Kshitij-1030/ClawMind/cad/xaxis.step

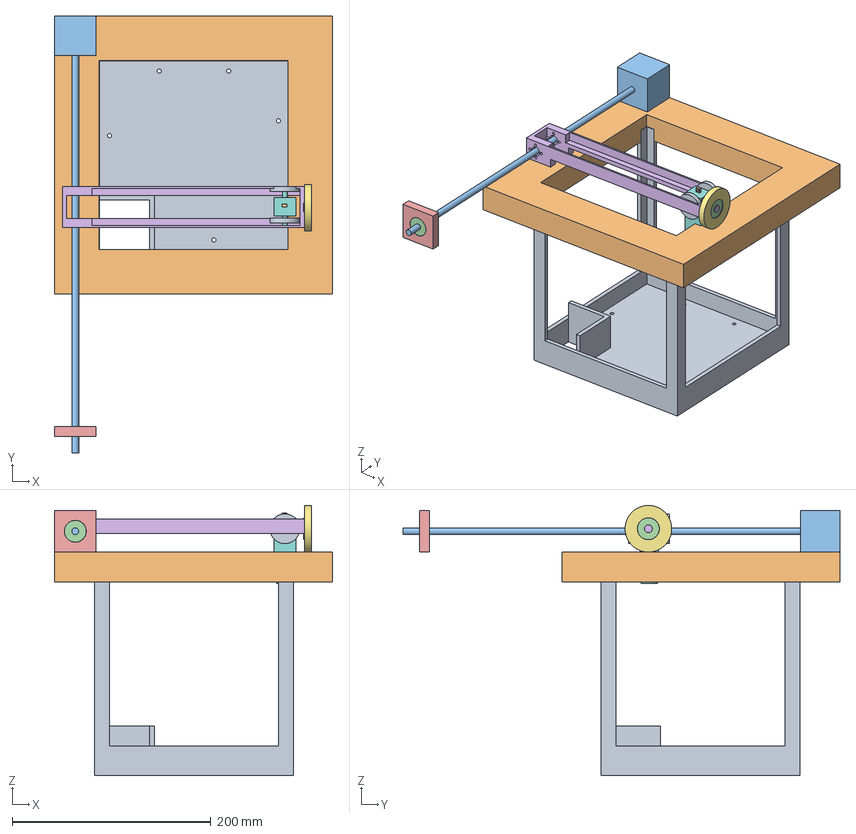
[picture p17: CAD file, 2026-04-23]
cad/xaxis.step
280.0 x 440.0 x 272.0 mm
